holmesrichards/QuantizerModule/hardware/Panel components/Unit 2.sch

## KiCad design hardware/Panel components/Unit 2.sch (2021-02-02, an earlier design)

Schematic: Unit 2.sch

Parts:
J17, J18, J19, J20, J21: AudioJack2_SwitchT
R21, R22, R23, R24, R25, R26, R27, R28, R29, R30, R31, R32, R33, R34, R35, R36: 1k
R37, R38, R39: 10k
R40: 100k
RV2: 100k; Potentiometer_Alpha_RD901F-40-00D_Single_Vertical_CircularH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
SW4, SW5: SW_Rotary12
SW6: SW_SPST; SPDT-toggle-switch-1M-series

Notes on the sheet:
Unit 2 controls and jacks — Duplicate of unit 1
