holmesrichards/QuantizerModule/hardware/Panel components/quantpc.sch

## KiCad design hardware/Panel components/quantpc.sch (2021-02-02, an earlier design)

Schematic: quantpc.sch

Parts:
J1, J2, J3, J4, J5, J6, J7, J8, J9, J12: MOLEX 2 PIN; Molex_KK-254_AE-6410-02A_1x02_P2.54mm_Vertical
J10, J11, J14, J15, J16: AudioJack2_SwitchT
J13: MOLEX 8 PIN; Molex_KK-254_AE-6410-08A_1x08_P2.54mm_Vertical
R1, R2, R3, R4, R5, R6, R7, R8, R9, R10, R11, R12, R13, R14, R15, R16: 1k
R17, R18, R19: 10k
R20: 100k
RV1: 100k; Potentiometer_Alpha_RD901F-40-00D_Single_Vertical_CircularH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
SW1: SW_SPST; SPDT-toggle-switch-1M-series
SW2, SW3: SW_Rotary12

Notes on the sheet:
to dac/ino CV IN A
to dac/ino CV IN B
to dac/ino GATE IN A
to dac/ino GATE IN B
to dac/ino CV OUT A
to dac/ino CV IN C
to dac/ino CV IN D
to dac/ino GATE IN C
to dac/ino GATE IN D
to dac/ino CV OUT B
Unit 1 controls and jacks — Duplicate for unit 2
Molex connectors
to dac/ino 8 pin Molex header
