holmesrichards/QuantizerModule/hardware/Panel/Panel.sch

## KiCad design hardware/Panel/Panel.sch (2020-06-08)

Schematic: Panel.sch

Parts:
H1, H2, H3, H4, H5, H6, H7, H8, H9, H10: MountingHole_Pad jack; Kosmo_Jack_Hole
H11, H12: MountingHole_Pad pot; Kosmo_Pot_Hole
H13, H14, H15, H16: MountingHole_Pad rotary; Kosmo_Jack_Hole
H17, H18: MountingHole_Pad toggle; Kosmo_Switch_Hole
H19, H20, H21, H22: MountingHole_Pad; Kosmo_Panel_Mounting_Hole
