holmesrichards/QuantizerModule/software/Quantizer/Quantizer.cpp

/*
 * Quantizer library
 * Rich Holmes
 * 
 * Based on:
 * TELEXo Eurorack Module
 * (c) 2016, 2017 Brendon Cassidy
 * MIT License
 */
 
//#include "Arduino.h"
#include "Quantizer.h"
//#include "TxHelper.h"

//
// initializes the quantizer and sets the scale to 0 (usually equal temperament)
//
Quantizer::Quantizer() {
  SetScale(0);
}

//
// initializes the quantizer and sets the initial scale
//
Quantizer::Quantizer(int scale) {
  SetScale(scale);  
}

//
// initializes the quantizer and sets the initial scale
//
Quantizer::Quantizer(int bank, int scale)
{
  SetScale(bank, scale);
}

/*
 * change the scale of the quantizer
 */
void Quantizer::SetScale(int scale) {
  if (scale >= 0 && scale < scaleCount)
    {
      _scale = scale;
      _last.Note = 0;
      _last.Value = 0;
 
      _below = 1;
      _above = 0;
    }
}

/*
 * change the scale of the quantizer
 */
void Quantizer::SetScale(int bank, int scale) {
  if (bank < 6 && scale < 12)
    SetScale (pgm_read_word(&bankandscale[bank][scale]));
}

/*
 * quantizes an int (range 0-DACTOP)
 */
QuantizeResponse Quantizer::Quantize(int in) {

  QuantizeResponse response;
  
  // deal with negative values
  in = in < 0 ? -in : in;

  // short circuit if we are within our current boundary
  if (in >= _below && in < _above){
    return _last;
  }
  
  // if not - we need to find where we are in the list
  // hints are a type of skip-list that jumps us to the proper octave
  _octave = (int)(in / DACPEROCTAVE) - 1;
  _octave = _octave > 0 ? _octave : 0;
  
  _index = pgm_read_word (&(hints[_scale][_octave]));
  
  int distance = 32767;
  int distanceTemp = 0;

  // find where we can't get any closer then back out
  while (_index < notecount[_scale]) {
    _temp = in - pgm_read_float (&(scales[_scale][_index]));
    
    distanceTemp = _temp < 0 ? -_temp : _temp;
    
    if (distanceTemp > distance){
      _index--;
      break;
    } else {
      // else increment
      distance = distanceTemp;
      _index++;
    }
    
  }

  // move it down to the next to last if we made it to the end
  if (_index >= notecount[_scale]) 
    _index = notecount[_scale] - 1;

  // use index to quantize
  _current = pgm_read_float (&(scales[_scale][_index])) + 0.5; // rounding

  // set the response
  response.Note = _index;
  response.Value = _current;
  
  _last = response;
  
  // now set the helper boundries
  _above = _index < notecount[_scale] - 1 ? pgm_read_float (&(scales[_scale][_index + 1])) : 32767;
  _below = _index > 0 ? pgm_read_float (&(scales[_scale][_index-1])) : pgm_read_float (&(scales[_scale][_index]));

  // similar to a mutable quantize trick to expand the region slightly
  // had been doing this using floats - thx for the fixed math tip oliver
  _above = ((13 * _current) + (19 * _above)) >> 5;
  _below = ((13 * _current) + (19 * _below)) >> 5;

  // constrain the above and below values
  _above = _above > 32767 ? 32767 : _above;
  _below = _below < 0 ? 0 : _below;

  return response;
  
}

/*
 * returns the values (0-16383) for a note number; 0 if out of range
 */
float Quantizer::GetValueForNote(int note){
  if (note < notecount[_scale])
    return pgm_read_float(&(scales[_scale][note]));
  else
    return 0;
}

// INSERT AUTOGENERATED SCALE CLASS DATA HERE
#if SCALESET == 0
// 0 | +e 12  |  12-equal chromatic
const float Quantizer::scale0[] = { 0.0,34.125,68.25,102.375,136.5,170.625,204.75,238.875,273.0,307.125,341.25,375.375,409.5,443.625,477.75,511.875,546.0,580.125,614.25,648.375,682.5,716.625,750.75,784.875,819.0,853.125,887.25,921.375,955.5,989.625,1023.75,1057.875,1092.0,1126.125,1160.25,1194.375,1228.5,1262.625,1296.75,1330.875,1365.0,1399.125,1433.25,1467.375,1501.5,1535.625,1569.75,1603.875,1638.0,1672.125,1706.25,1740.375,1774.5,1808.625,1842.75,1876.875,1911.0,1945.125,1979.25,2013.375,2047.5 };
const int Quantizer::hints0[] = { 0,12,24,36,48,60 };
// 1 | +e 12 0 2 4 5 7 9 11  | major
const float Quantizer::scale1[] = { 0.0,68.25,136.5,170.625,238.875,307.125,375.375,409.5,477.75,546.0,580.125,648.375,716.625,784.875,819.0,887.25,955.5,989.625,1057.875,1126.125,1194.375,1228.5,1296.75,1365.0,1399.125,1467.375,1535.625,1603.875,1638.0,1706.25,1774.5,1808.625,1876.875,1945.125,2013.375,2047.5 };
const int Quantizer::hints1[] = { 0,7,14,21,28,35 };
// 2 | +e 12 0 2 3 5 7 8 10  | natural minor
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
const int Quantizer::hints64[] = { 0,3,6,9,12,15 };
// 65 | +e 12 0 4 7 10  |  dominant seventh
const float Quantizer::scale65[] = { 0.0,136.5,238.875,341.25,409.5,546.0,648.375,750.75,819.0,955.5,1057.875,1160.25,1228.5,1365.0,1467.375,1569.75,1638.0,1774.5,1876.875,1979.25,2047.5 };
const int Quantizer::hints65[] = { 0,4,8,12,16,20 };

const int Quantizer::notecount[] = { 61,36,61,36,66,216,26,36,61,86,26,36,61,96,156,26,36,61,96,26,36,61,61,61,61,61,61,61,61,61,61,61,61,61,6,11,16,21,26,31,36,41,46,51,56,66,71,76,81,86,91,96,101,106,111,116,121,36,36,36,26,26,31,16,16,21 };

const float *Quantizer::scales[] = { scale0,scale1,scale2,scale3,scale4,scale5,scale6,scale7,scale8,scale9,scale10,scale11,scale12,scale13,scale14,scale15,scale16,scale17,scale18,scale19,scale20,scale21,scale22,scale23,scale24,scale25,scale26,scale27,scale28,scale29,scale30,scale31,scale32,scale33,scale34,scale35,scale36,scale37,scale38,scale39,scale40,scale41,scale42,scale43,scale44,scale45,scale46,scale47,scale48,scale49,scale50,scale51,scale52,scale53,scale54,scale55,scale56,scale57,scale58,scale59,scale60,scale61,scale62,scale63,scale64,scale65 };
const int *Quantizer::hints[] = { hints0,hints1,hints2,hints3,hints4,hints5,hints6,hints7,hints8,hints9,hints10,hints11,hints12,hints13,hints14,hints15,hints16,hints17,hints18,hints19,hints20,hints21,hints22,hints23,hints24,hints25,hints26,hints27,hints28,hints29,hints30,hints31,hints32,hints33,hints34,hints35,hints36,hints37,hints38,hints39,hints40,hints41,hints42,hints43,hints44,hints45,hints46,hints47,hints48,hints49,hints50,hints51,hints52,hints53,hints54,hints55,hints56,hints57,hints58,hints59,hints60,hints61,hints62,hints63,hints64,hints65 };


const int Quantizer::bankandscale[6][12] = {
  {   0,  57,  58,  59,  60,  61,  62,  39,  63,  64,  65,  37 }, //  1  Top Twelve
  {   1,   2,   3,   4,   5,  -1,  -1,  -1,   6,   7,   8,   9 }, //  2  Just/Pythagorean
  {  10,  11,  12,  13,  14,  15,  16,  17,  18,  19,  20,  21 }, //  3  Meantone
  {  22,  23,  24,  25,  26,  27,  28,  29,  30,  31,  32,  33 }, //  4  Well temperaments
  {  34,  35,  36,  37,  38,  39,  40,  41,  42,  43,  44,   0 }, //  5  Macrotonal (and 12-note) equal divisions
  {  45,  46,  47,  48,  49,  50,  51,  52,  53,  54,  55,  56 }  //  6  Microtonal equal divisions
};
#endif
// END AUTOGENERATED SCALE CLASS DATA
